AchimPieters/ESP8266-HomeKit-Fountain-light/Images/1.jpeg

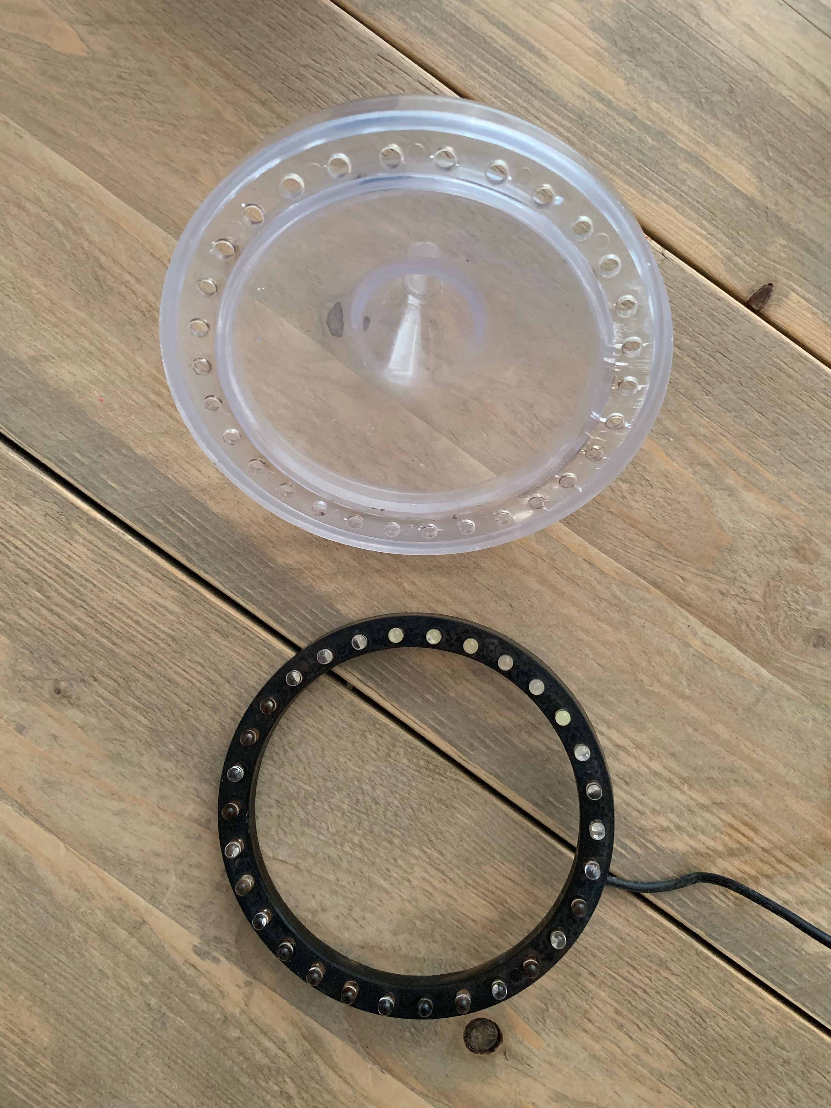
Images/1.jpeg
