AchimPieters/ESP8266-HomeKit-Fountain-light/Images/2.jpeg

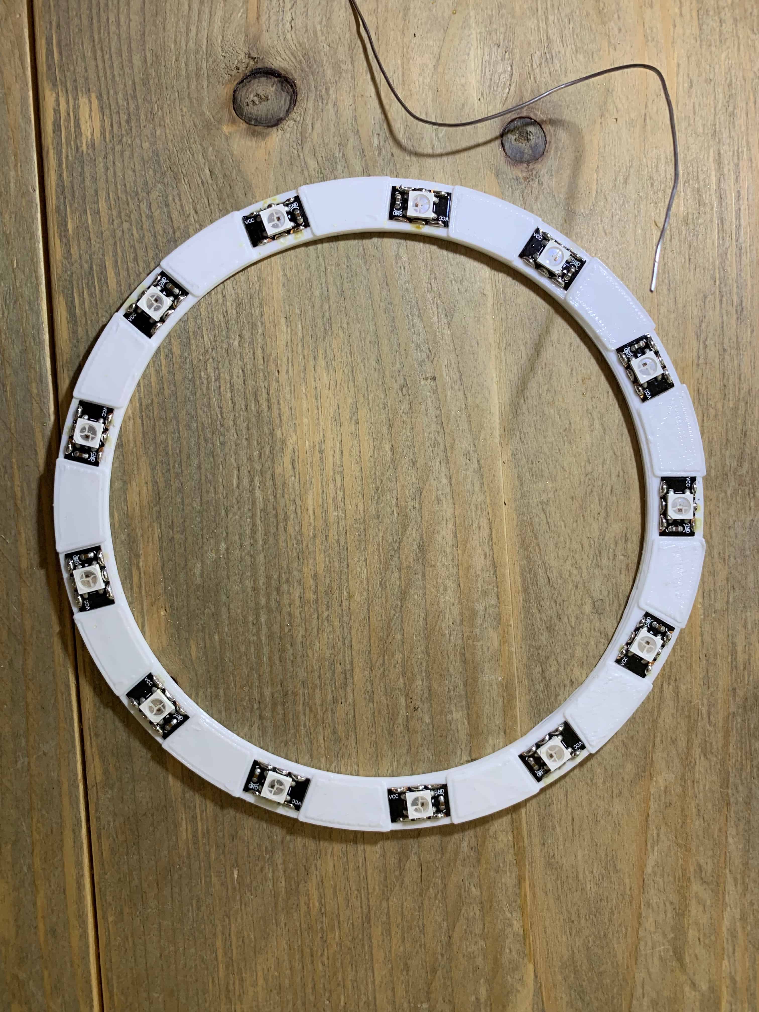
Images/2.jpeg
