AchimPieters/ESP8266-HomeKit-Fountain-light/Images/3.jpeg

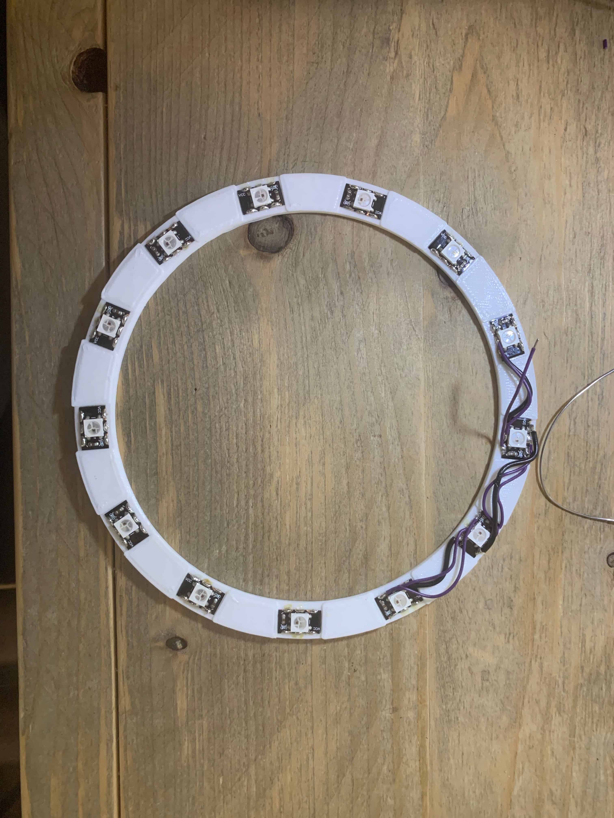
Images/3.jpeg
