AchimPieters/ESP8266-HomeKit-Fountain-light/Images/4.jpeg

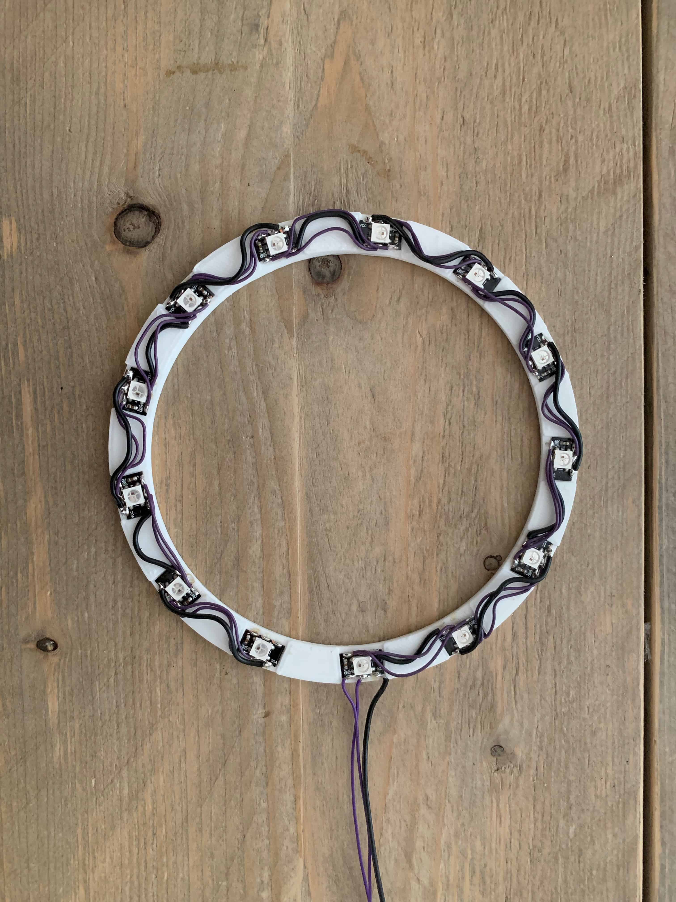
Images/4.jpeg
