AchimPieters/ESP8266-HomeKit-Fountain-light/Images/5.jpeg

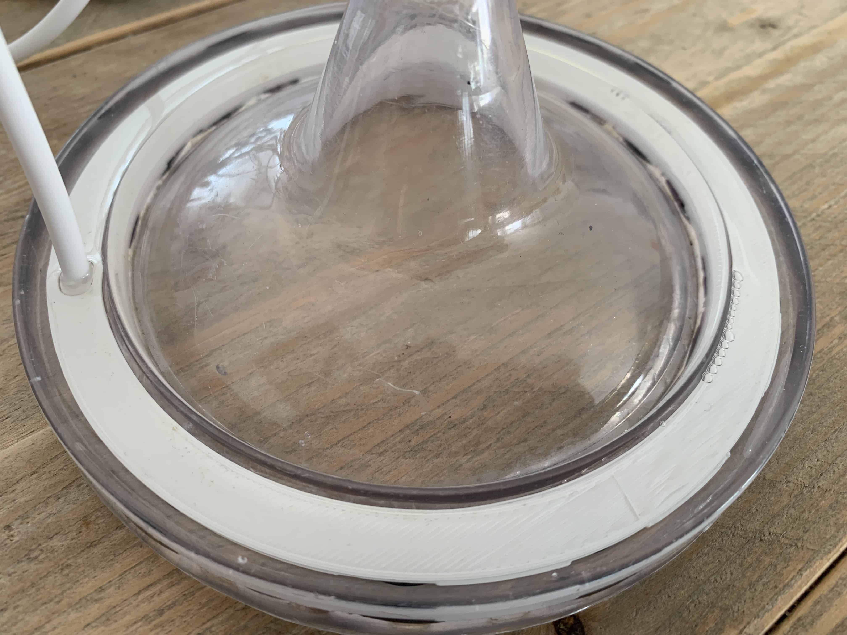
Images/5.jpeg
