AchimPieters/ESP8266-HomeKit-Fountain-light/Images/6.jpeg

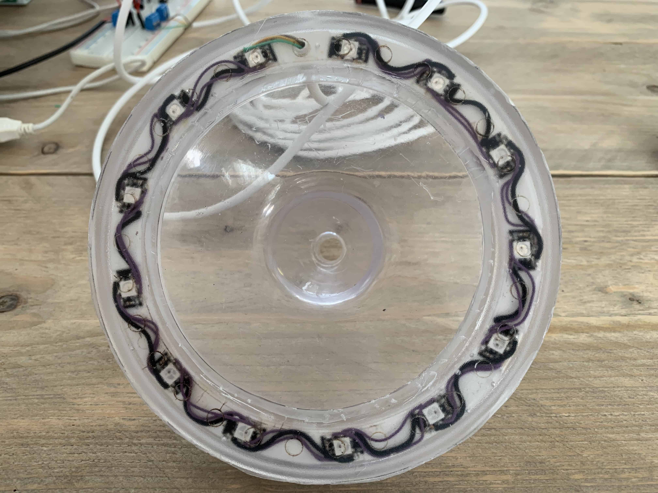
Images/6.jpeg
