AchimPieters/ESP8266-HomeKit-Fountain-light/Images/8.png

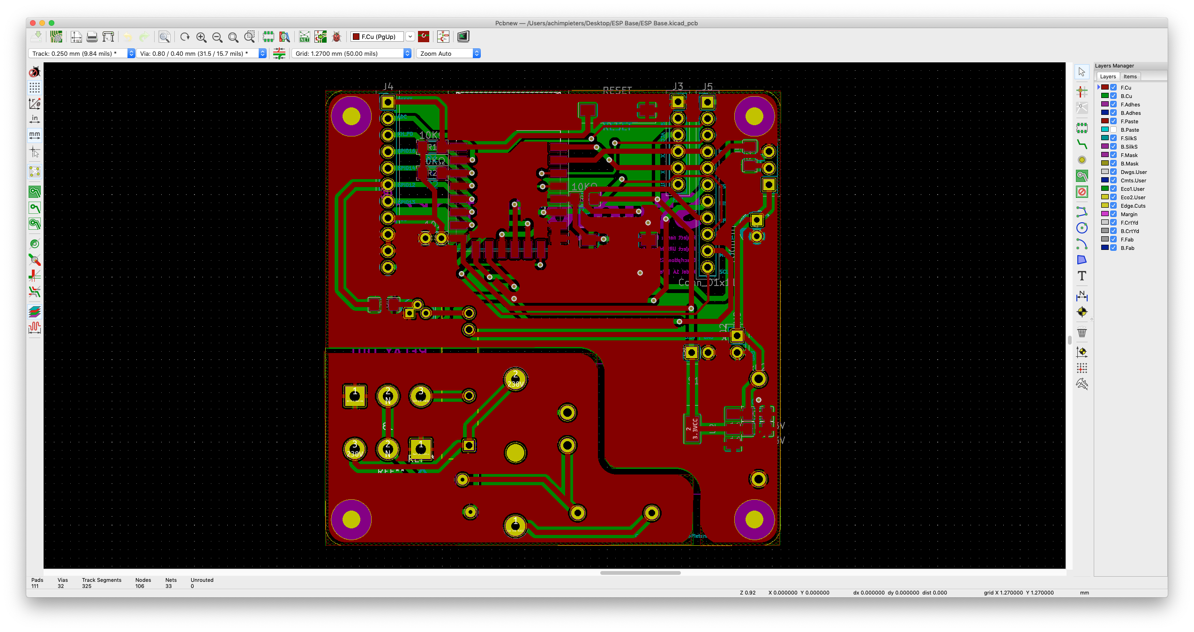
Images/8.png
