AchimPieters/ESP8266-HomeKit-Fountain-light/Images/9.JPEG

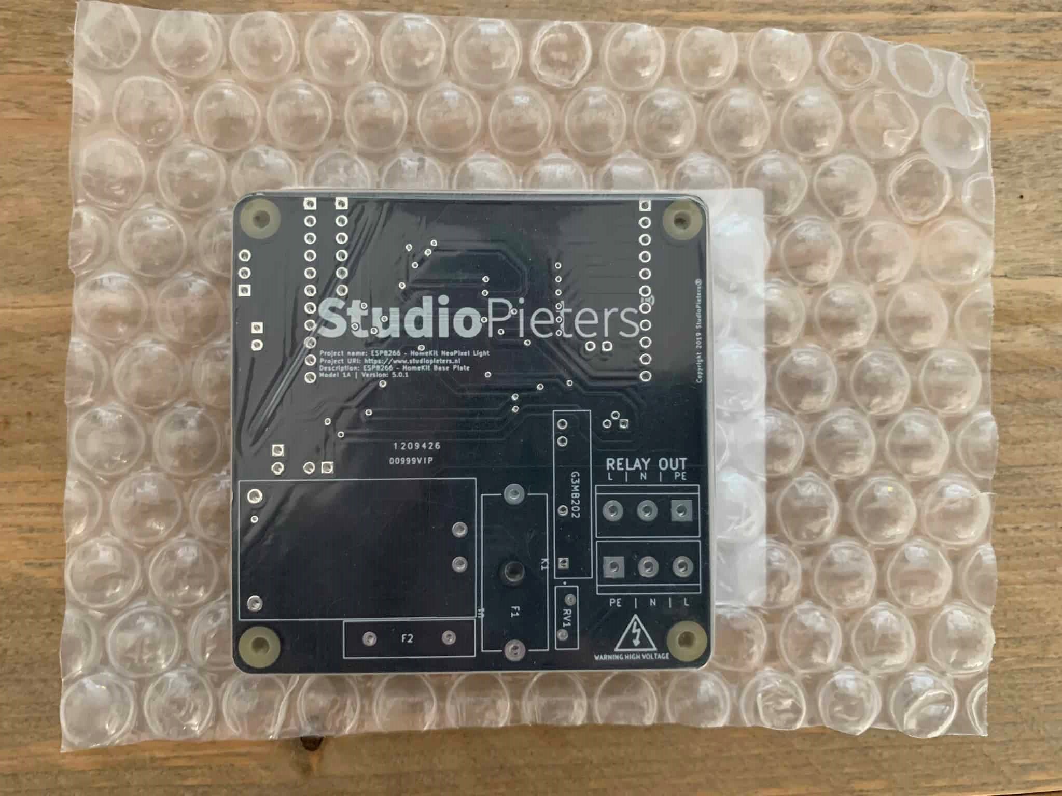
Images/9.JPEG
