AchimPieters/ESP8266-HomeKit-Fountain-light/Images/10.JPEG

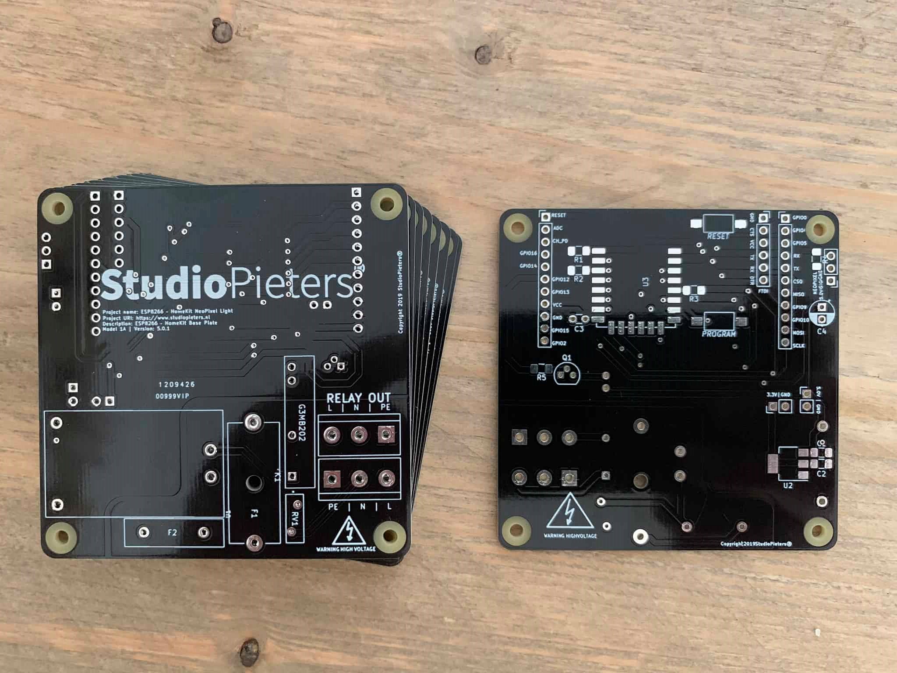
Images/10.JPEG
