AchimPieters/ESP8266-HomeKit-Fountain-light/Images/11.JPEG

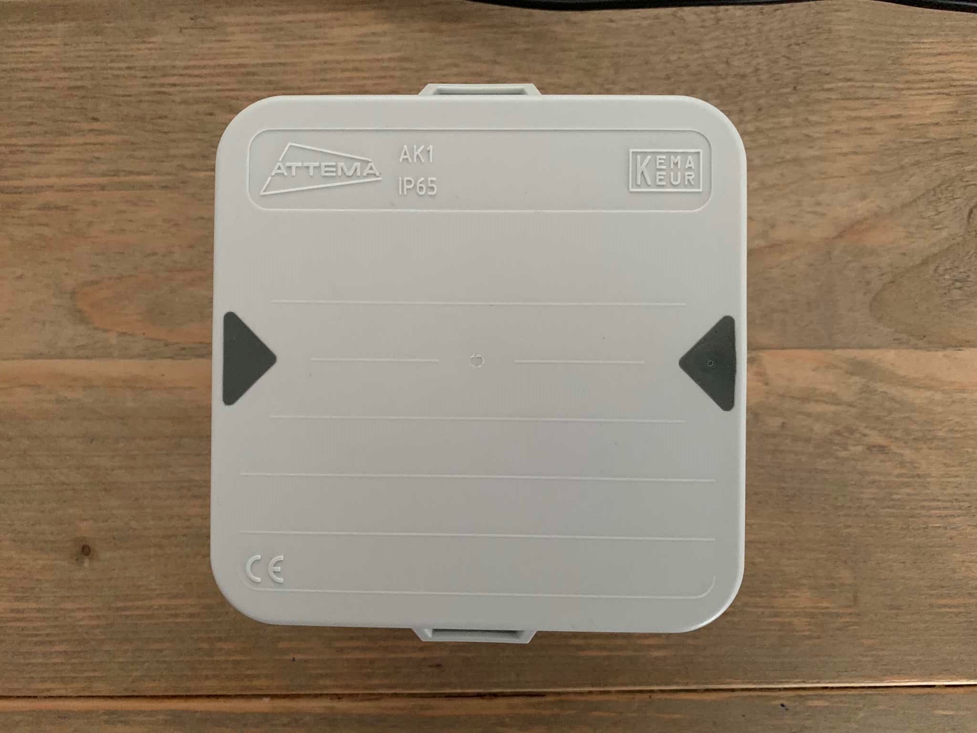
Images/11.JPEG
