AchimPieters/ESP8266-HomeKit-Fountain-light/Images/12.JPEG

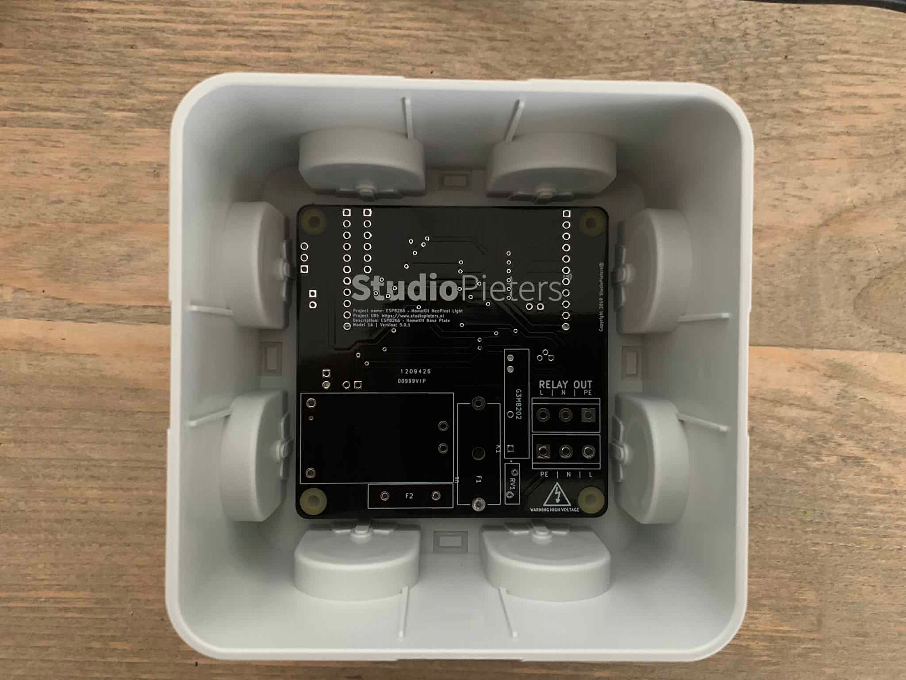
Images/12.JPEG
