AchimPieters/ESP8266-HomeKit-Fountain-light/Images/13.JPEG

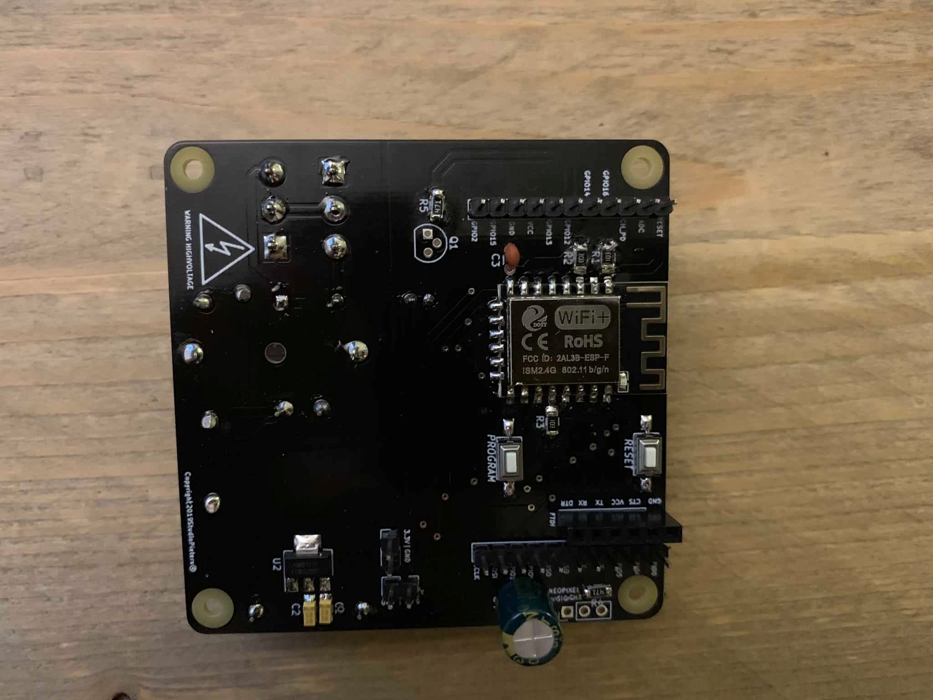
Images/13.JPEG
