AchimPieters/ESP8266-HomeKit-Fountain-light/Images/14.JPEG

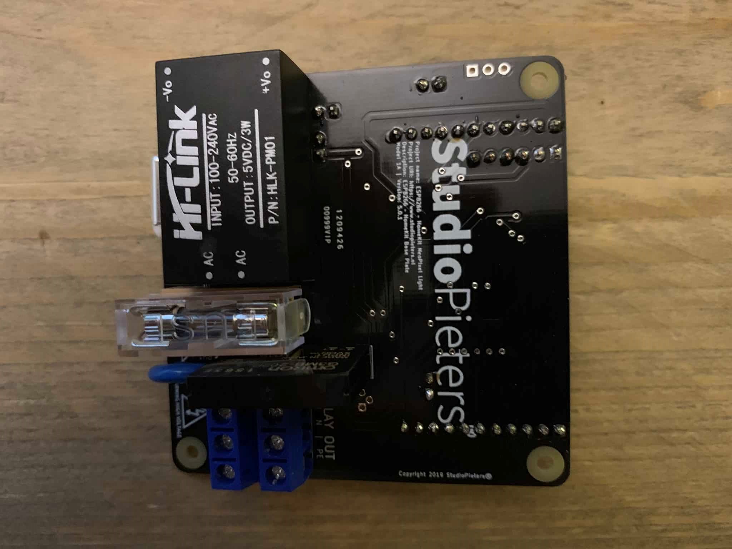
Images/14.JPEG
