AchimPieters/ESP8266-HomeKit-Fountain-light/Images/15.JPEG

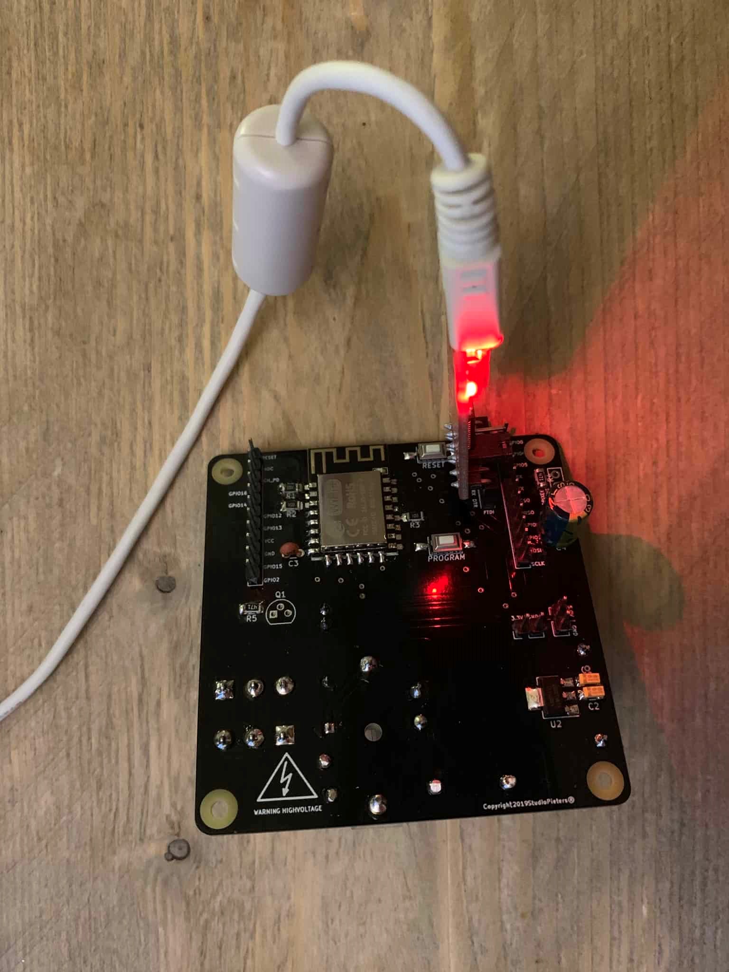
Images/15.JPEG
