AchimPieters/ESP8266-HomeKit-Fountain-light/Images/16.jpeg

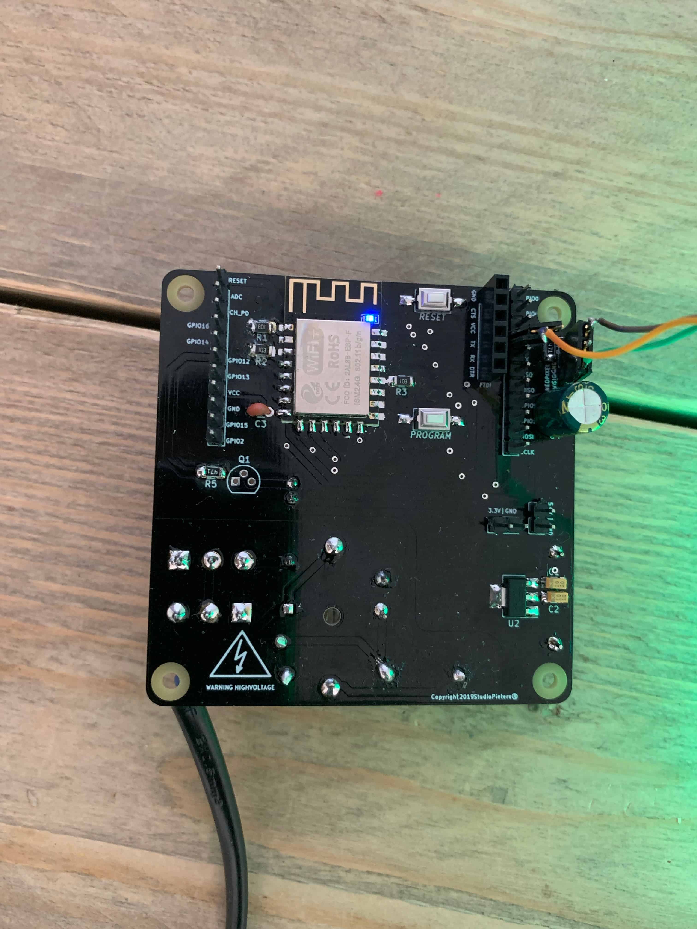
Images/16.jpeg
