AchimPieters/ESP8266-HomeKit-Fountain-light/Images/17.jpeg

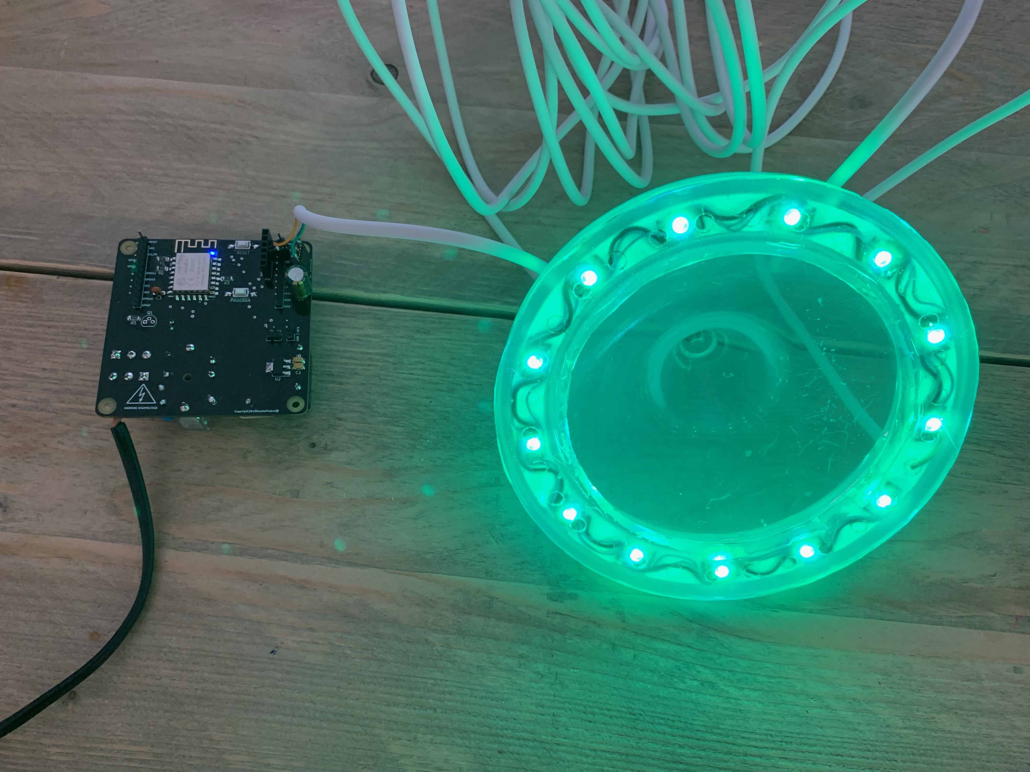
Images/17.jpeg
