AchimPieters/ESP8266-HomeKit-Fountain-light/Images/18.jpg

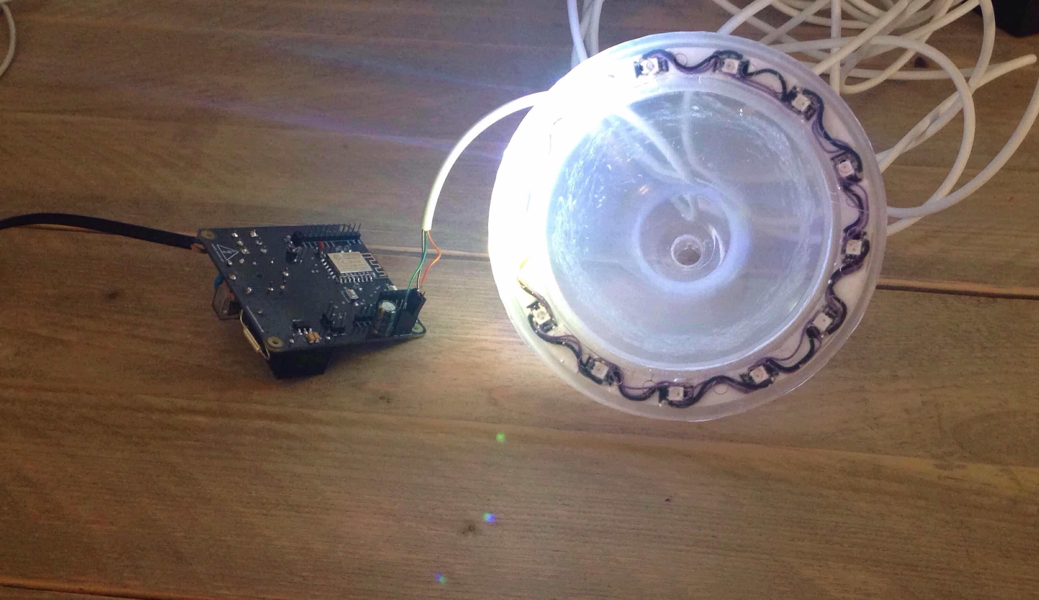
Images/18.jpg
