AchimPieters/ESP8266-HomeKit-Fountain-light/Images/19.jpeg

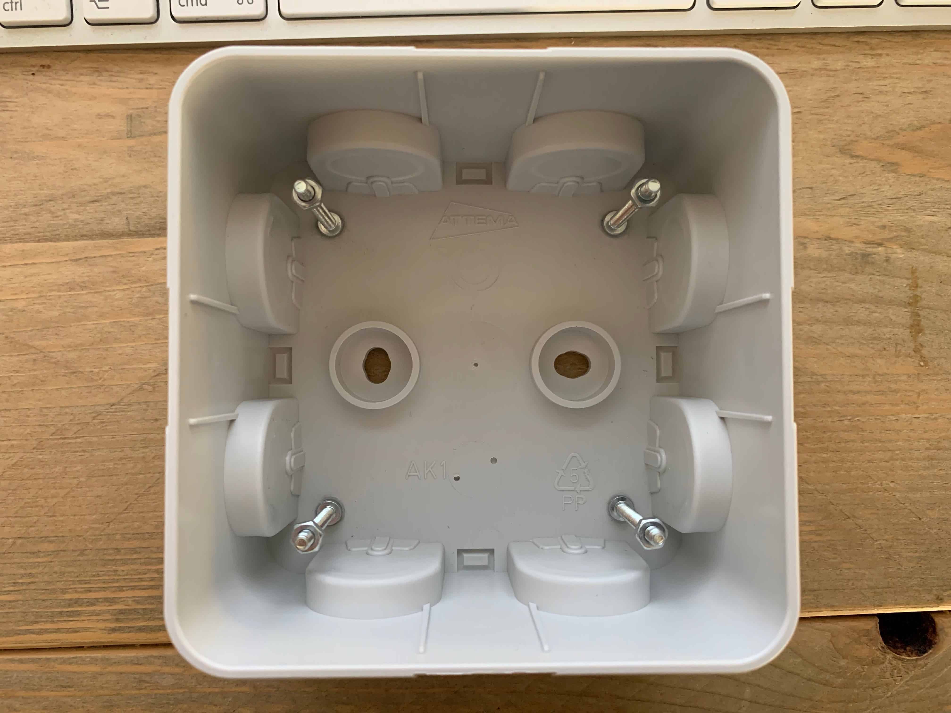
Images/19.jpeg
