AchimPieters/ESP8266-HomeKit-Fountain-light/Images/20.jpeg

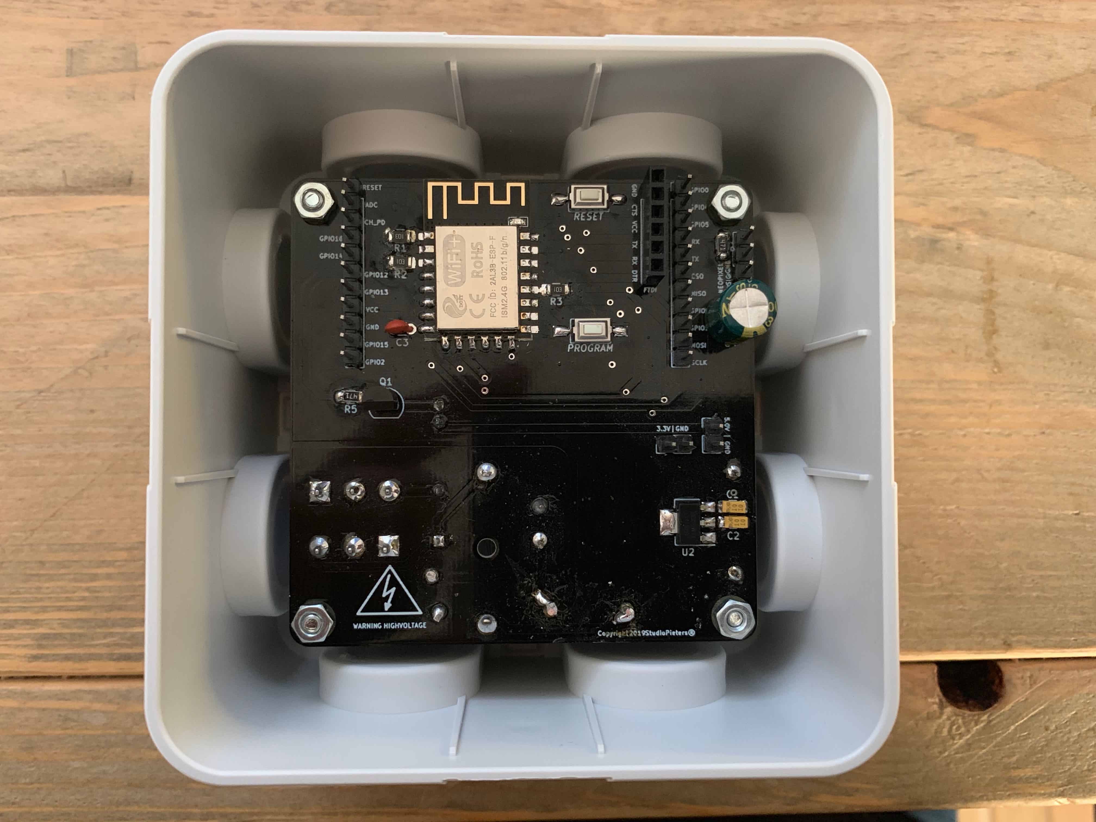
Images/20.jpeg
